MUBARIS-KT/DC-DC_CONVERTER/swg.png

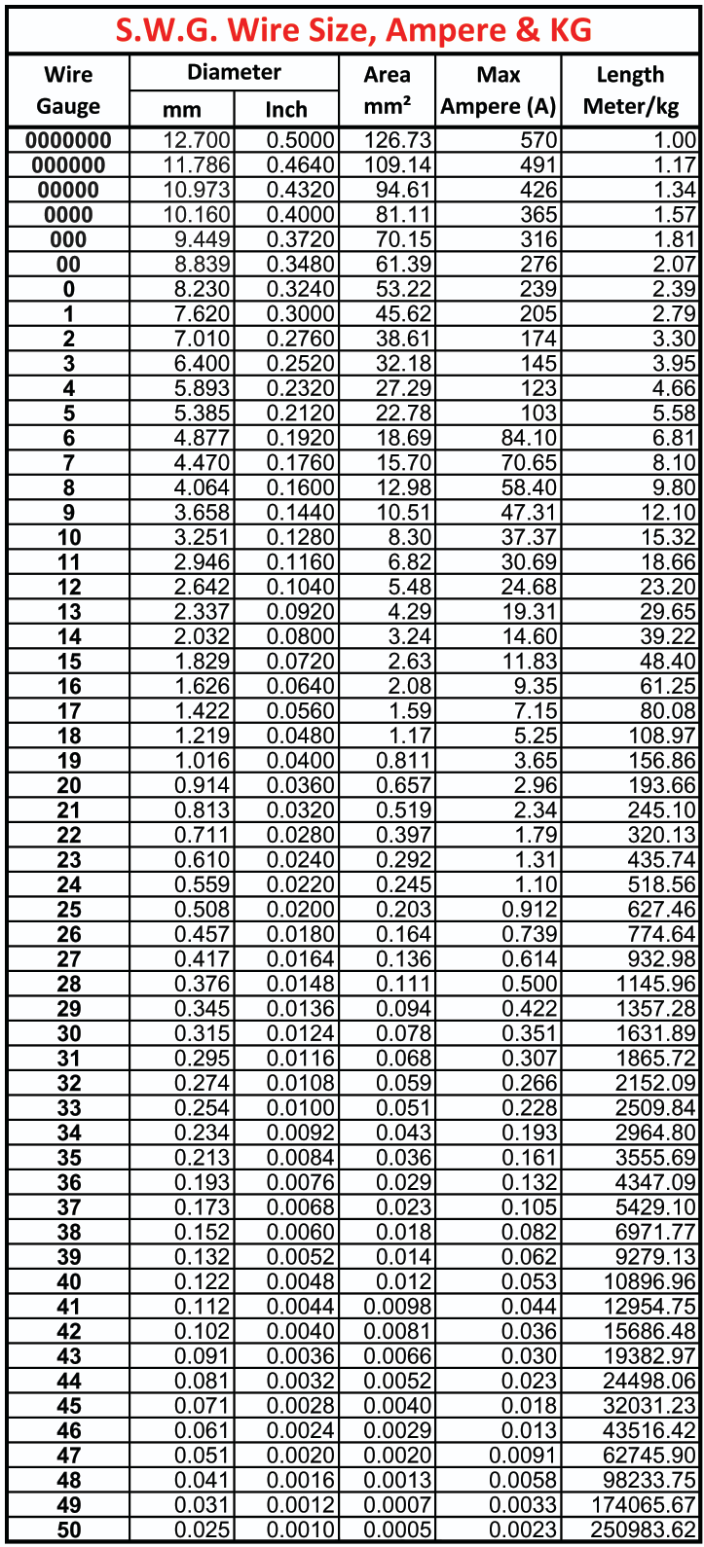
swg.png
