MUBARIS-KT/DC-DC_CONVERTER/SWG_chart.png

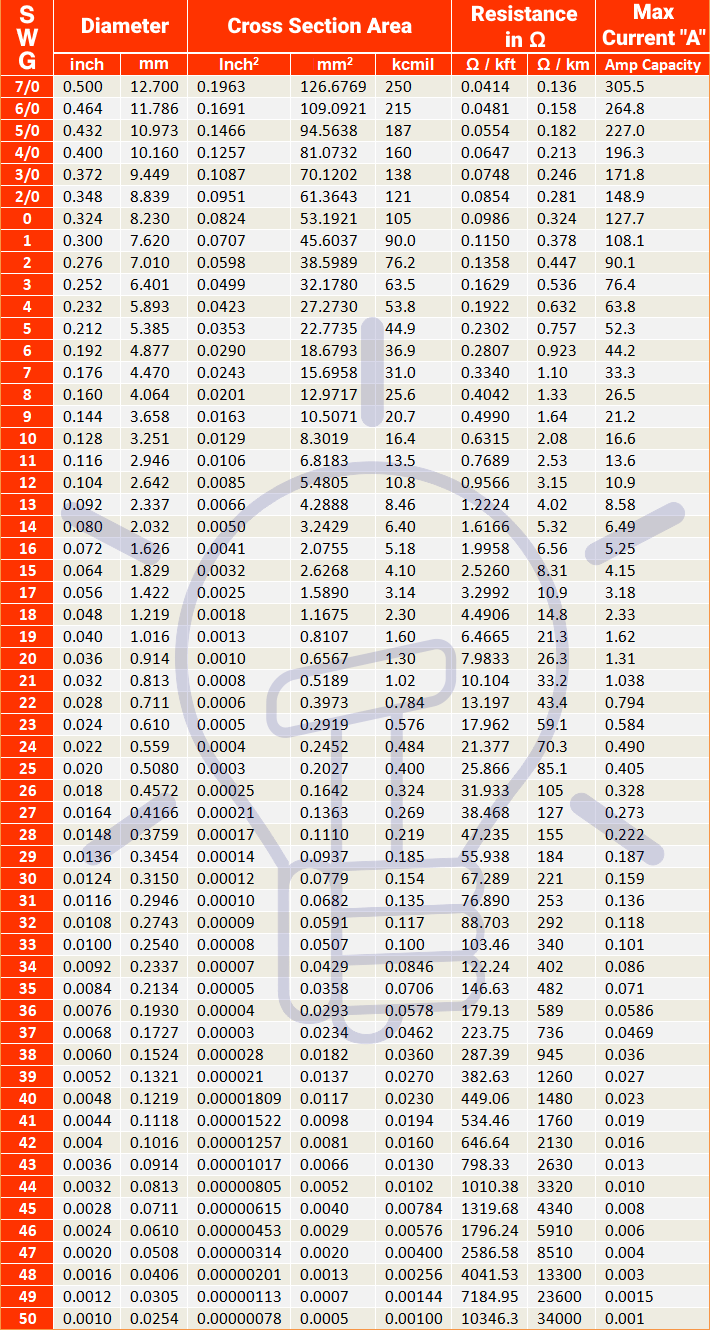
SWG_chart.png
