MUBARIS-KT/DC-DC_CONVERTER/Gate Driver TLP152 V1.1/sed.pdf

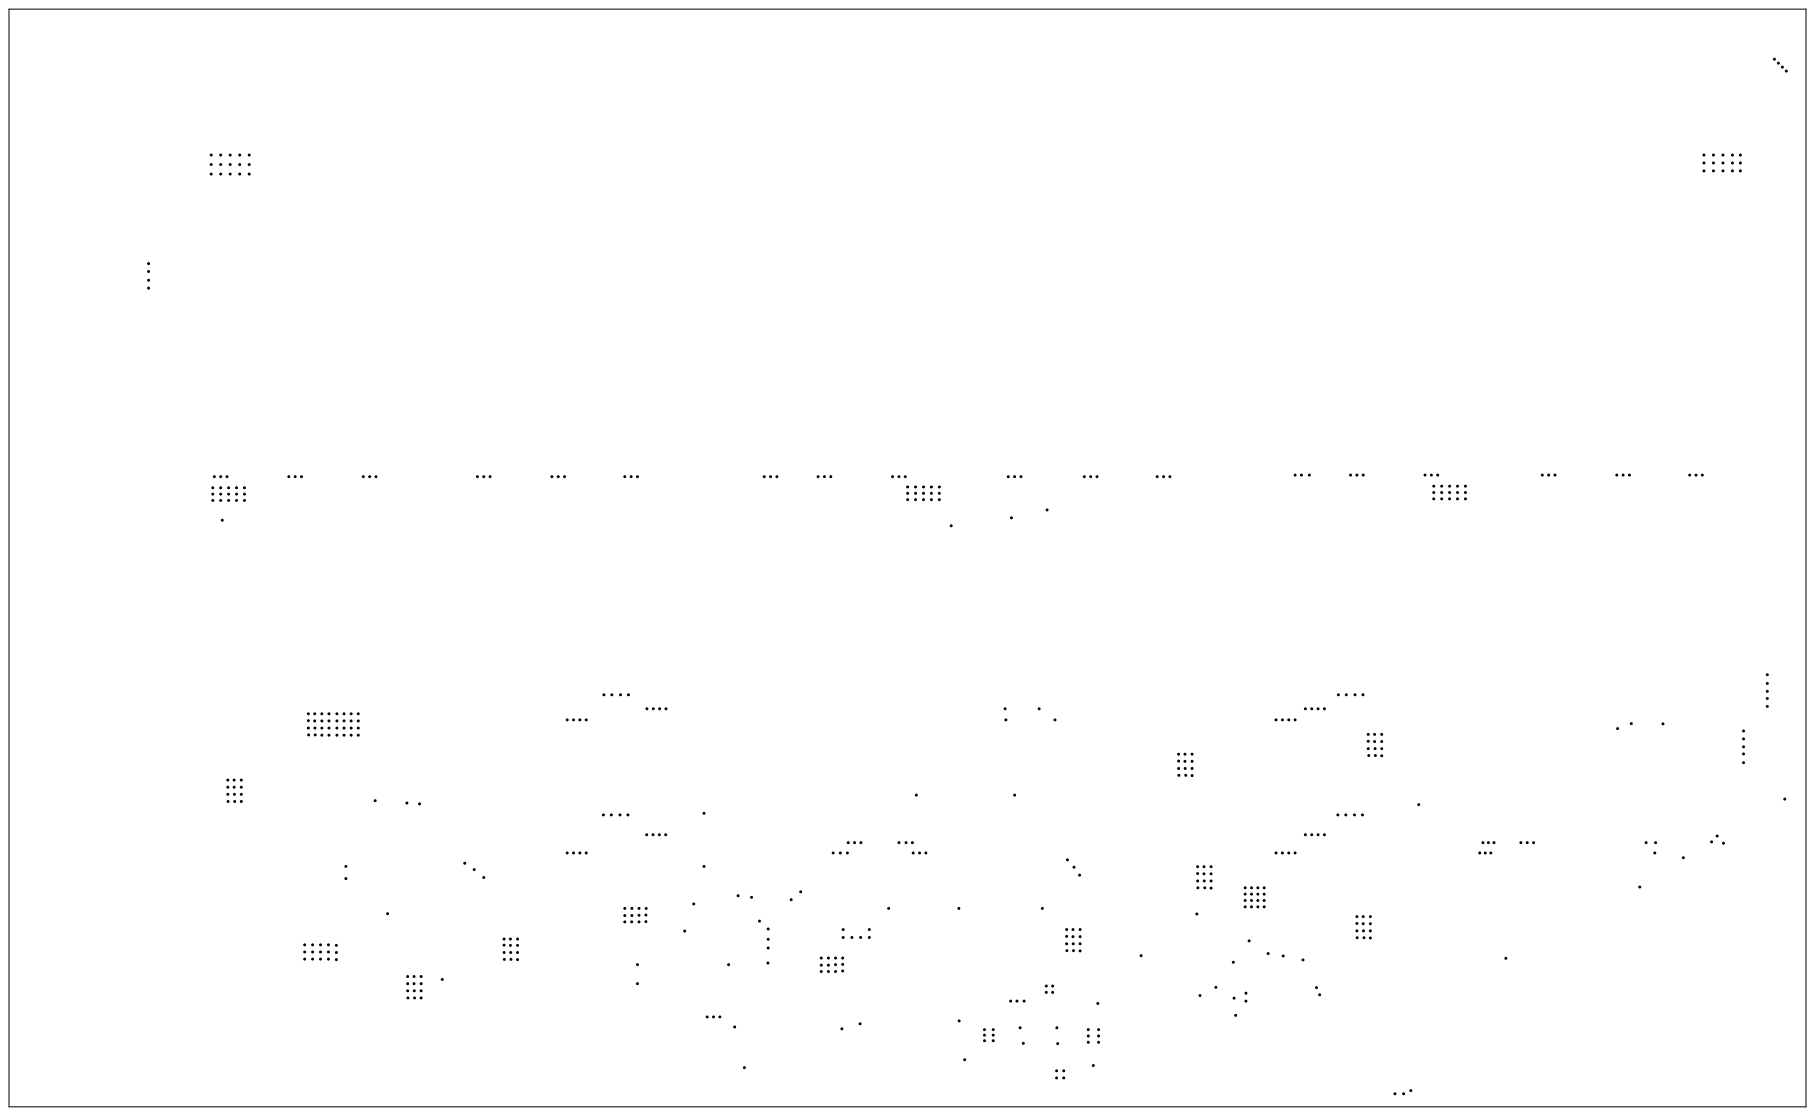
[picture p85: page 1]
