MUBARIS-KT/DC-DC_CONVERTER/PWM/pwm_ert_rtw/pwm.c

/*
 * Academic License - for use in teaching, academic research, and meeting
 * course requirements at degree granting institutions only.  Not for
 * government, commercial, or other organizational use.
 *
 * File: pwm.c
 *
 * Code generated for Simulink model 'pwm'.
 *
 * Model version                  : 1.6
 * Simulink Coder version         : 24.1 (R2024a) 19-Nov-2023
 * C/C++ source code generated on : Thu Aug  8 16:41:47 2024
 *
 * Target selection: ert.tlc
 * Embedded hardware selection: Texas Instruments->C2000
 * Code generation objectives: Unspecified
 * Validation result: Not run
 */

#include "pwm.h"
#include "rtwtypes.h"
#include "pwm_private.h"

/* Block signals (default storage) */
B_pwm_T pwm_B;

/* Real-time model */
static RT_MODEL_pwm_T pwm_M_;
RT_MODEL_pwm_T *const pwm_M = &pwm_M_;

#ifndef __TMS320C28XX_CLA__

uint16_T MW_adcBInitFlag = 0;

#endif

/* Model step function */
void pwm_step(void)
{
  real_T rtb_Sum;

  /* S-Function (c2802xadc): '<Root>/ADC' */
  {
    /*  Internal Reference Voltage : Fixed scale 0 to 3.3 V range.  */
    /*  External Reference Voltage : Allowable ranges of VREFHI(ADCINA0) = 3.3 and VREFLO(tied to ground) = 0  */
    AdcbRegs.ADCSOCFRC1.bit.SOC0 = 1U;

    /* Wait for the period of Sampling window and EOC result to be latched after trigger */
#ifndef __TMS320C28XX_CLA__

    asm(" RPT #75|| NOP");

#endif

#ifdef __TMS320C28XX_CLA__

    real32_T wait_index;
    for (wait_index= 12; wait_index > 0; wait_index--)
      __mnop();

#endif

    pwm_B.ADC = (AdcbResultRegs.ADCRESULT0);
  }

  /* Gain: '<Root>/Gain' */
  rtb_Sum = pwm_P.Gain_Gain * pwm_B.ADC;

  /* S-Function (c2802xpwm): '<Root>/ePWM' */

  /*-- Update CMPA value for ePWM1 --*/
  {
    EPwm1Regs.CMPA.bit.CMPA = (uint16_T)((uint32_T)EPwm1Regs.TBPRD * rtb_Sum *
      0.01);
  }

  /* Sum: '<Root>/Sum' incorporates:
   *  Constant: '<Root>/Constant'
   */
  rtb_Sum = pwm_P.Constant_Value - rtb_Sum;

  /* S-Function (c2802xpwm): '<Root>/ePWM1' */

  /*-- Update CMPA value for ePWM2 --*/
  {
    EPwm2Regs.CMPA.bit.CMPA = (uint16_T)((uint32_T)EPwm2Regs.TBPRD * rtb_Sum *
      0.01);
  }
}

/* Model initialize function */
void pwm_initialize(void)
{
  /* Registration code */

  /* initialize error status */
  rtmSetErrorStatus(pwm_M, (NULL));

  /* block I/O */
  (void) memset(((void *) &pwm_B), 0,
                sizeof(B_pwm_T));

  /* Start for S-Function (c2802xadc): '<Root>/ADC' */
  if (MW_adcBInitFlag == 0U) {
    InitAdcB();
    MW_adcBInitFlag = 1U;
  }

  config_ADCB_SOC0 ();

  /* Start for S-Function (c2802xpwm): '<Root>/ePWM' */

  /*** Initialize ePWM1 modules ***/
  {
    /*  // Time Base Control Register
       EPwm1Regs.TBCTL.bit.CTRMODE              = 2U;          // Counter Mode
       EPwm1Regs.TBCTL.bit.SYNCOSEL             = 1U;          // Sync Output Select

       EPwm1Regs.TBCTL.bit.PRDLD                = 0U;          // Shadow select

       EPwm1Regs.TBCTL2.bit.PRDLDSYNC           = 0U;          // Shadow select

       EPwm1Regs.TBCTL.bit.PHSEN                = 0U;          // Phase Load Enable
       EPwm1Regs.TBCTL.bit.PHSDIR               = 0U;          // Phase Direction Bit
       EPwm1Regs.TBCTL.bit.HSPCLKDIV            = 0U;          // High Speed TBCLK Pre-scaler
       EPwm1Regs.TBCTL.bit.CLKDIV               = 0U;          // Time Base Clock Pre-scaler
     */
    EPwm1Regs.TBCTL.all = (EPwm1Regs.TBCTL.all & ~0x3FFFU) | 0x12U;
    EPwm1Regs.TBCTL2.all = (EPwm1Regs.TBCTL2.all & ~0xC000U) | 0x0U;

    /*-- Setup Time-Base (TB) Submodule --*/
    EPwm1Regs.TBPRD = 1667U;           // Time Base Period Register

    /* // Time-Base Phase Register
       EPwm1Regs.TBPHS.bit.TBPHS               = 0U;          // Phase offset register
     */
    EPwm1Regs.TBPHS.all = (EPwm1Regs.TBPHS.all & ~0xFFFF0000U) | 0x0U;

    // Time Base Counter Register
    EPwm1Regs.TBCTR = 0x0000U;         /* Clear counter*/

    /*-- Setup Counter_Compare (CC) Submodule --*/
    /*	// Counter Compare Control Register

       EPwm1Regs.CMPCTL.bit.LOADASYNC           = 0U;          // Active Compare A Load SYNC Option
       EPwm1Regs.CMPCTL.bit.LOADBSYNC           = 0U;          // Active Compare B Load SYNC Option
       EPwm1Regs.CMPCTL.bit.LOADAMODE           = 0U;          // Active Compare A Load
       EPwm1Regs.CMPCTL.bit.LOADBMODE           = 0U;          // Active Compare B Load
       EPwm1Regs.CMPCTL.bit.SHDWAMODE           = 0U;          // Compare A Register Block Operating Mode
       EPwm1Regs.CMPCTL.bit.SHDWBMODE           = 0U;          // Compare B Register Block Operating Mode
     */
    EPwm1Regs.CMPCTL.all = (EPwm1Regs.CMPCTL.all & ~0x3C5FU) | 0x0U;

    /* EPwm1Regs.CMPCTL2.bit.SHDWCMODE           = 0U;          // Compare C Register Block Operating Mode
       EPwm1Regs.CMPCTL2.bit.SHDWDMODE           = 0U;          // Compare D Register Block Operating Mode
       EPwm1Regs.CMPCTL2.bit.LOADCSYNC           = 0U;          // Active Compare C Load SYNC Option
       EPwm1Regs.CMPCTL2.bit.LOADDSYNC           = 0U;          // Active Compare D Load SYNC Option
       EPwm1Regs.CMPCTL2.bit.LOADCMODE           = 0U;          // Active Compare C Load
       EPwm1Regs.CMPCTL2.bit.LOADDMODE           = 0U;          // Active Compare D Load
     */
    EPwm1Regs.CMPCTL2.all = (EPwm1Regs.CMPCTL2.all & ~0x3C5FU) | 0x0U;
    EPwm1Regs.CMPA.bit.CMPA = 833U;    // Counter Compare A Register
    EPwm1Regs.CMPB.bit.CMPB = 833U;    // Counter Compare B Register
    EPwm1Regs.CMPC = 32000U;           // Counter Compare C Register
    EPwm1Regs.CMPD = 32000U;           // Counter Compare D Register

    /*-- Setup Action-Qualifier (AQ) Submodule --*/
    EPwm1Regs.AQCTLA.all = 144U;
                               // Action Qualifier Control Register For Output A
    EPwm1Regs.AQCTLB.all = 144U;
                               // Action Qualifier Control Register For Output B

    /*	// Action Qualifier Software Force Register
       EPwm1Regs.AQSFRC.bit.RLDCSF              = 0U;          // Reload from Shadow Options
     */
    EPwm1Regs.AQSFRC.all = (EPwm1Regs.AQSFRC.all & ~0xC0U) | 0x0U;

    /*	// Action Qualifier Continuous S/W Force Register
       EPwm1Regs.AQCSFRC.bit.CSFA               = 0U;          // Continuous Software Force on output A
       EPwm1Regs.AQCSFRC.bit.CSFB               = 0U;          // Continuous Software Force on output B
     */
    EPwm1Regs.AQCSFRC.all = (EPwm1Regs.AQCSFRC.all & ~0xFU) | 0x0U;

    /*-- Setup Dead-Band Generator (DB) Submodule --*/
    /*	// Dead-Band Generator Control Register
       EPwm1Regs.DBCTL.bit.OUT_MODE             = 0U;          // Dead Band Output Mode Control
       EPwm1Regs.DBCTL.bit.IN_MODE              = 0U;          // Dead Band Input Select Mode Control
       EPwm1Regs.DBCTL.bit.POLSEL               = 0;          // Polarity Select Control
       EPwm1Regs.DBCTL.bit.HALFCYCLE            = 0U;          // Half Cycle Clocking Enable
       EPwm1Regs.DBCTL.bit.SHDWDBREDMODE        = 0U;          // DBRED shadow mode
       EPwm1Regs.DBCTL.bit.SHDWDBFEDMODE        = 0U;          // DBFED shadow mode
       EPwm1Regs.DBCTL.bit.LOADREDMODE          = 4U;        // DBRED load
       EPwm1Regs.DBCTL.bit.LOADFEDMODE          = 4U;        // DBFED load
     */
    EPwm1Regs.DBCTL.all = (EPwm1Regs.DBCTL.all & ~0x8FFFU) | 0x0U;
    EPwm1Regs.DBRED.bit.DBRED = (uint16_T)(0);
                         // Dead-Band Generator Rising Edge Delay Count Register
    EPwm1Regs.DBFED.bit.DBFED = (uint16_T)(0);
                        // Dead-Band Generator Falling Edge Delay Count Register

    /*-- Setup Event-Trigger (ET) Submodule --*/
    /*	// Event Trigger Selection and Pre-Scale Register
       EPwm1Regs.ETSEL.bit.SOCAEN               = 0U;          // Start of Conversion A Enable
       EPwm1Regs.ETSEL.bit.SOCASELCMP           = 0U;
       EPwm1Regs.ETSEL.bit.SOCASEL              = 1U;          // Start of Conversion A Select
       EPwm1Regs.ETPS.bit.SOCPSSEL              = 1U;          // EPWM1SOC Period Select
       EPwm1Regs.ETSOCPS.bit.SOCAPRD2           = 1U;
       EPwm1Regs.ETSEL.bit.SOCBEN               = 0U;          // Start of Conversion B Enable
       EPwm1Regs.ETSEL.bit.SOCBSELCMP           = 0U;
       EPwm1Regs.ETSEL.bit.SOCBSEL              = 1U;          // Start of Conversion A Select
       EPwm1Regs.ETPS.bit.SOCPSSEL              = 1;          // EPWM1SOCB Period Select
       EPwm1Regs.ETSOCPS.bit.SOCBPRD2           = 1U;
       EPwm1Regs.ETSEL.bit.INTEN                = 0U;          // EPWM1INTn Enable
       EPwm1Regs.ETSEL.bit.INTSELCMP            = 0U;
       EPwm1Regs.ETSEL.bit.INTSEL               = 1U;          // Start of Conversion A Select
       EPwm1Regs.ETPS.bit.INTPSSEL              = 1U;          // EPWM1INTn Period Select
       EPwm1Regs.ETINTPS.bit.INTPRD2            = 1U;
     */
    EPwm1Regs.ETSEL.all = (EPwm1Regs.ETSEL.all & ~0xFF7FU) | 0x1101U;
    EPwm1Regs.ETPS.all = (EPwm1Regs.ETPS.all & ~0x30U) | 0x30U;
    EPwm1Regs.ETSOCPS.all = (EPwm1Regs.ETSOCPS.all & ~0xF0FU) | 0x101U;
    EPwm1Regs.ETINTPS.all = (EPwm1Regs.ETINTPS.all & ~0xFU) | 0x1U;

    /*-- Setup PWM-Chopper (PC) Submodule --*/
    /*	// PWM Chopper Control Register
       EPwm1Regs.PCCTL.bit.CHPEN                = 0U;          // PWM chopping enable
       EPwm1Regs.PCCTL.bit.CHPFREQ              = 0U;          // Chopping clock frequency
       EPwm1Regs.PCCTL.bit.OSHTWTH              = 0U;          // One-shot pulse width
       EPwm1Regs.PCCTL.bit.CHPDUTY              = 0U;          // Chopping clock Duty cycle
     */
    EPwm1Regs.PCCTL.all = (EPwm1Regs.PCCTL.all & ~0x7FFU) | 0x0U;

    /*-- Set up Trip-Zone (TZ) Submodule --*/
    EALLOW;
    EPwm1Regs.TZSEL.all = 0U;          // Trip Zone Select Register

    /*	// Trip Zone Control Register
       EPwm1Regs.TZCTL.bit.TZA                  = 3U;          // TZ1 to TZ6 Trip Action On EPWM1A
       EPwm1Regs.TZCTL.bit.TZB                  = 3U;          // TZ1 to TZ6 Trip Action On EPWM1B
       EPwm1Regs.TZCTL.bit.DCAEVT1              = 3U;          // EPWM1A action on DCAEVT1
       EPwm1Regs.TZCTL.bit.DCAEVT2              = 3U;          // EPWM1A action on DCAEVT2
       EPwm1Regs.TZCTL.bit.DCBEVT1              = 3U;          // EPWM1B action on DCBEVT1
       EPwm1Regs.TZCTL.bit.DCBEVT2              = 3U;          // EPWM1B action on DCBEVT2
     */
    EPwm1Regs.TZCTL.all = (EPwm1Regs.TZCTL.all & ~0xFFFU) | 0xFFFU;

    /*	// Trip Zone Enable Interrupt Register
       EPwm1Regs.TZEINT.bit.OST                 = 0U;          // Trip Zones One Shot Int Enable
       EPwm1Regs.TZEINT.bit.CBC                 = 0U;          // Trip Zones Cycle By Cycle Int Enable
       EPwm1Regs.TZEINT.bit.DCAEVT1             = 0U;          // Digital Compare A Event 1 Int Enable
       EPwm1Regs.TZEINT.bit.DCAEVT2             = 0U;          // Digital Compare A Event 2 Int Enable
       EPwm1Regs.TZEINT.bit.DCBEVT1             = 0U;          // Digital Compare B Event 1 Int Enable
       EPwm1Regs.TZEINT.bit.DCBEVT2             = 0U;          // Digital Compare B Event 2 Int Enable
     */
    EPwm1Regs.TZEINT.all = (EPwm1Regs.TZEINT.all & ~0x7EU) | 0x0U;

    /*	// Digital Compare A Control Register
       EPwm1Regs.DCACTL.bit.EVT1SYNCE           = 0U;          // DCAEVT1 SYNC Enable
       EPwm1Regs.DCACTL.bit.EVT1SOCE            = 1U;          // DCAEVT1 SOC Enable
       EPwm1Regs.DCACTL.bit.EVT1FRCSYNCSEL      = 0U;          // DCAEVT1 Force Sync Signal
       EPwm1Regs.DCACTL.bit.EVT1SRCSEL          = 0U;          // DCAEVT1 Source Signal
       EPwm1Regs.DCACTL.bit.EVT2FRCSYNCSEL      = 0U;          // DCAEVT2 Force Sync Signal
       EPwm1Regs.DCACTL.bit.EVT2SRCSEL          = 0U;          // DCAEVT2 Source Signal
     */
    EPwm1Regs.DCACTL.all = (EPwm1Regs.DCACTL.all & ~0x30FU) | 0x4U;

    /*	// Digital Compare B Control Register
       EPwm1Regs.DCBCTL.bit.EVT1SYNCE           = 0U;          // DCBEVT1 SYNC Enable
       EPwm1Regs.DCBCTL.bit.EVT1SOCE            = 0U;          // DCBEVT1 SOC Enable
       EPwm1Regs.DCBCTL.bit.EVT1FRCSYNCSEL      = 0U;          // DCBEVT1 Force Sync Signal
       EPwm1Regs.DCBCTL.bit.EVT1SRCSEL          = 0U;          // DCBEVT1 Source Signal
       EPwm1Regs.DCBCTL.bit.EVT2FRCSYNCSEL      = 0U;          // DCBEVT2 Force Sync Signal
       EPwm1Regs.DCBCTL.bit.EVT2SRCSEL          = 0U;          // DCBEVT2 Source Signal
     */
    EPwm1Regs.DCBCTL.all = (EPwm1Regs.DCBCTL.all & ~0x30FU) | 0x0U;

    /*	// Digital Compare Trip Select Register
       EPwm1Regs.DCTRIPSEL.bit.DCAHCOMPSEL      = 0U;          // Digital Compare A High COMP Input Select

       EPwm1Regs.DCTRIPSEL.bit.DCALCOMPSEL      = 0U;          // Digital Compare A Low COMP Input Select
       EPwm1Regs.DCTRIPSEL.bit.DCBHCOMPSEL      = 0U;          // Digital Compare B High COMP Input Select
       EPwm1Regs.DCTRIPSEL.bit.DCBLCOMPSEL      = 0U;          // Digital Compare B Low COMP Input Select
     */
    EPwm1Regs.DCTRIPSEL.all = (EPwm1Regs.DCTRIPSEL.all & ~ 0xFFFFU) | 0x0U;

    /*	// Trip Zone Digital Comparator Select Register
       EPwm1Regs.TZDCSEL.bit.DCAEVT1            = 0U;          // Digital Compare Output A Event 1
       EPwm1Regs.TZDCSEL.bit.DCAEVT2            = 0U;          // Digital Compare Output A Event 2
       EPwm1Regs.TZDCSEL.bit.DCBEVT1            = 0U;          // Digital Compare Output B Event 1
       EPwm1Regs.TZDCSEL.bit.DCBEVT2            = 0U;          // Digital Compare Output B Event 2
     */
    EPwm1Regs.TZDCSEL.all = (EPwm1Regs.TZDCSEL.all & ~0xFFFU) | 0x0U;

    /*	// Digital Compare Filter Control Register
       EPwm1Regs.DCFCTL.bit.BLANKE              = 0U;          // Blanking Enable/Disable
       EPwm1Regs.DCFCTL.bit.PULSESEL            = 1U;          // Pulse Select for Blanking & Capture Alignment
       EPwm1Regs.DCFCTL.bit.BLANKINV            = 0U;          // Blanking Window Inversion
       EPwm1Regs.DCFCTL.bit.SRCSEL              = 0U;          // Filter Block Signal Source Select
     */
    EPwm1Regs.DCFCTL.all = (EPwm1Regs.DCFCTL.all & ~0x3FU) | 0x10U;
    EPwm1Regs.DCFOFFSET = 0U;          // Digital Compare Filter Offset Register
    EPwm1Regs.DCFWINDOW = 0U;          // Digital Compare Filter Window Register

    /*	// Digital Compare Capture Control Register
       EPwm1Regs.DCCAPCTL.bit.CAPE              = 0U;          // Counter Capture Enable
     */
    EPwm1Regs.DCCAPCTL.all = (EPwm1Regs.DCCAPCTL.all & ~0x1U) | 0x0U;

    /*	// HRPWM Configuration Register
       EPwm1Regs.HRCNFG.bit.SWAPAB              = 0U;          // Swap EPWMA and EPWMB Outputs Bit
       EPwm1Regs.HRCNFG.bit.SELOUTB             = 0U;          // EPWMB Output Selection Bit
     */
    EPwm1Regs.HRCNFG.all = (EPwm1Regs.HRCNFG.all & ~0xA0U) | 0x0U;

    /* Update the Link Registers with the link value for all the Compare values and TBPRD */
    /* No error is thrown if the ePWM register exists in the model or not */
    EPwm1Regs.EPWMXLINK.bit.TBPRDLINK = 0U;
    EPwm1Regs.EPWMXLINK.bit.CMPALINK = 0U;
    EPwm1Regs.EPWMXLINK.bit.CMPBLINK = 0U;
    EPwm1Regs.EPWMXLINK.bit.CMPCLINK = 0U;
    EPwm1Regs.EPWMXLINK.bit.CMPDLINK = 0U;

    /* SYNCPER - Peripheral synchronization output event
       EPwm1Regs.HRPCTL.bit.PWMSYNCSEL            = 1U;          // EPWMSYNCPER selection
       EPwm1Regs.HRPCTL.bit.PWMSYNCSELX           = 0U;          //  EPWMSYNCPER selection
     */
    EPwm1Regs.HRPCTL.all = (EPwm1Regs.HRPCTL.all & ~0x72U) | 0x2U;
    EDIS;
  }

  /* Start for S-Function (c2802xpwm): '<Root>/ePWM1' */

  /*** Initialize ePWM2 modules ***/
  {
    /*  // Time Base Control Register
       EPwm2Regs.TBCTL.bit.CTRMODE              = 2U;          // Counter Mode
       EPwm2Regs.TBCTL.bit.SYNCOSEL             = 0U;          // Sync Output Select

       EPwm2Regs.TBCTL.bit.PRDLD                = 0U;          // Shadow select

       EPwm2Regs.TBCTL2.bit.PRDLDSYNC           = 0U;          // Shadow select

       EPwm2Regs.TBCTL.bit.PHSEN                = 1U;          // Phase Load Enable
       EPwm2Regs.TBCTL.bit.PHSDIR               = 1U;          // Phase Direction Bit
       EPwm2Regs.TBCTL.bit.HSPCLKDIV            = 0U;          // High Speed TBCLK Pre-scaler
       EPwm2Regs.TBCTL.bit.CLKDIV               = 0U;          // Time Base Clock Pre-scaler
     */
    EPwm2Regs.TBCTL.all = (EPwm2Regs.TBCTL.all & ~0x3FFFU) | 0x2006U;
    EPwm2Regs.TBCTL2.all = (EPwm2Regs.TBCTL2.all & ~0xC000U) | 0x0U;

    /*-- Setup Time-Base (TB) Submodule --*/
    EPwm2Regs.TBPRD = 1667U;           // Time Base Period Register

    /* // Time-Base Phase Register
       EPwm2Regs.TBPHS.bit.TBPHS               = 0U;          // Phase offset register
     */
    EPwm2Regs.TBPHS.all = (EPwm2Regs.TBPHS.all & ~0xFFFF0000U) | 0x0U;

    // Time Base Counter Register
    EPwm2Regs.TBCTR = 0x0000U;         /* Clear counter*/

    /*-- Setup Counter_Compare (CC) Submodule --*/
    /*	// Counter Compare Control Register

       EPwm2Regs.CMPCTL.bit.LOADASYNC           = 0U;          // Active Compare A Load SYNC Option
       EPwm2Regs.CMPCTL.bit.LOADBSYNC           = 0U;          // Active Compare B Load SYNC Option
       EPwm2Regs.CMPCTL.bit.LOADAMODE           = 0U;          // Active Compare A Load
       EPwm2Regs.CMPCTL.bit.LOADBMODE           = 0U;          // Active Compare B Load
       EPwm2Regs.CMPCTL.bit.SHDWAMODE           = 0U;          // Compare A Register Block Operating Mode
       EPwm2Regs.CMPCTL.bit.SHDWBMODE           = 0U;          // Compare B Register Block Operating Mode
     */
    EPwm2Regs.CMPCTL.all = (EPwm2Regs.CMPCTL.all & ~0x3C5FU) | 0x0U;

    /* EPwm2Regs.CMPCTL2.bit.SHDWCMODE           = 0U;          // Compare C Register Block Operating Mode
       EPwm2Regs.CMPCTL2.bit.SHDWDMODE           = 0U;          // Compare D Register Block Operating Mode
       EPwm2Regs.CMPCTL2.bit.LOADCSYNC           = 0U;          // Active Compare C Load SYNC Option
       EPwm2Regs.CMPCTL2.bit.LOADDSYNC           = 0U;          // Active Compare D Load SYNC Option
       EPwm2Regs.CMPCTL2.bit.LOADCMODE           = 0U;          // Active Compare C Load
       EPwm2Regs.CMPCTL2.bit.LOADDMODE           = 0U;          // Active Compare D Load
     */
    EPwm2Regs.CMPCTL2.all = (EPwm2Regs.CMPCTL2.all & ~0x3C5FU) | 0x0U;
    EPwm2Regs.CMPA.bit.CMPA = 833U;    // Counter Compare A Register
    EPwm2Regs.CMPB.bit.CMPB = 833U;    // Counter Compare B Register
    EPwm2Regs.CMPC = 32000U;           // Counter Compare C Register
    EPwm2Regs.CMPD = 32000U;           // Counter Compare D Register

    /*-- Setup Action-Qualifier (AQ) Submodule --*/
    EPwm2Regs.AQCTLA.all = 96U;// Action Qualifier Control Register For Output A
    EPwm2Regs.AQCTLB.all = 96U;// Action Qualifier Control Register For Output B

    /*	// Action Qualifier Software Force Register
       EPwm2Regs.AQSFRC.bit.RLDCSF              = 0U;          // Reload from Shadow Options
     */
    EPwm2Regs.AQSFRC.all = (EPwm2Regs.AQSFRC.all & ~0xC0U) | 0x0U;

    /*	// Action Qualifier Continuous S/W Force Register
       EPwm2Regs.AQCSFRC.bit.CSFA               = 0U;          // Continuous Software Force on output A
       EPwm2Regs.AQCSFRC.bit.CSFB               = 0U;          // Continuous Software Force on output B
     */
    EPwm2Regs.AQCSFRC.all = (EPwm2Regs.AQCSFRC.all & ~0xFU) | 0x0U;

    /*-- Setup Dead-Band Generator (DB) Submodule --*/
    /*	// Dead-Band Generator Control Register
       EPwm2Regs.DBCTL.bit.OUT_MODE             = 0U;          // Dead Band Output Mode Control
       EPwm2Regs.DBCTL.bit.IN_MODE              = 0U;          // Dead Band Input Select Mode Control
       EPwm2Regs.DBCTL.bit.POLSEL               = 0;          // Polarity Select Control
       EPwm2Regs.DBCTL.bit.HALFCYCLE            = 0U;          // Half Cycle Clocking Enable
       EPwm2Regs.DBCTL.bit.SHDWDBREDMODE        = 0U;          // DBRED shadow mode
       EPwm2Regs.DBCTL.bit.SHDWDBFEDMODE        = 0U;          // DBFED shadow mode
       EPwm2Regs.DBCTL.bit.LOADREDMODE          = 4U;        // DBRED load
       EPwm2Regs.DBCTL.bit.LOADFEDMODE          = 4U;        // DBFED load
     */
    EPwm2Regs.DBCTL.all = (EPwm2Regs.DBCTL.all & ~0x8FFFU) | 0x0U;
    EPwm2Regs.DBRED.bit.DBRED = (uint16_T)(0);
                         // Dead-Band Generator Rising Edge Delay Count Register
    EPwm2Regs.DBFED.bit.DBFED = (uint16_T)(0);
                        // Dead-Band Generator Falling Edge Delay Count Register

    /*-- Setup Event-Trigger (ET) Submodule --*/
    /*	// Event Trigger Selection and Pre-Scale Register
       EPwm2Regs.ETSEL.bit.SOCAEN               = 0U;          // Start of Conversion A Enable
       EPwm2Regs.ETSEL.bit.SOCASELCMP           = 0U;
       EPwm2Regs.ETSEL.bit.SOCASEL              = 1U;          // Start of Conversion A Select
       EPwm2Regs.ETPS.bit.SOCPSSEL              = 1U;          // EPWM2SOC Period Select
       EPwm2Regs.ETSOCPS.bit.SOCAPRD2           = 1U;
       EPwm2Regs.ETSEL.bit.SOCBEN               = 0U;          // Start of Conversion B Enable
       EPwm2Regs.ETSEL.bit.SOCBSELCMP           = 0U;
       EPwm2Regs.ETSEL.bit.SOCBSEL              = 1U;          // Start of Conversion A Select
       EPwm2Regs.ETPS.bit.SOCPSSEL              = 1;          // EPWM2SOCB Period Select
       EPwm2Regs.ETSOCPS.bit.SOCBPRD2           = 1U;
       EPwm2Regs.ETSEL.bit.INTEN                = 0U;          // EPWM2INTn Enable
       EPwm2Regs.ETSEL.bit.INTSELCMP            = 0U;
       EPwm2Regs.ETSEL.bit.INTSEL               = 1U;          // Start of Conversion A Select
       EPwm2Regs.ETPS.bit.INTPSSEL              = 1U;          // EPWM2INTn Period Select
       EPwm2Regs.ETINTPS.bit.INTPRD2            = 1U;
     */
    EPwm2Regs.ETSEL.all = (EPwm2Regs.ETSEL.all & ~0xFF7FU) | 0x1101U;
    EPwm2Regs.ETPS.all = (EPwm2Regs.ETPS.all & ~0x30U) | 0x30U;
    EPwm2Regs.ETSOCPS.all = (EPwm2Regs.ETSOCPS.all & ~0xF0FU) | 0x101U;
    EPwm2Regs.ETINTPS.all = (EPwm2Regs.ETINTPS.all & ~0xFU) | 0x1U;

    /*-- Setup PWM-Chopper (PC) Submodule --*/
    /*	// PWM Chopper Control Register
       EPwm2Regs.PCCTL.bit.CHPEN                = 0U;          // PWM chopping enable
       EPwm2Regs.PCCTL.bit.CHPFREQ              = 0U;          // Chopping clock frequency
       EPwm2Regs.PCCTL.bit.OSHTWTH              = 0U;          // One-shot pulse width
       EPwm2Regs.PCCTL.bit.CHPDUTY              = 0U;          // Chopping clock Duty cycle
     */
    EPwm2Regs.PCCTL.all = (EPwm2Regs.PCCTL.all & ~0x7FFU) | 0x0U;

    /*-- Set up Trip-Zone (TZ) Submodule --*/
    EALLOW;
    EPwm2Regs.TZSEL.all = 0U;          // Trip Zone Select Register

    /*	// Trip Zone Control Register
       EPwm2Regs.TZCTL.bit.TZA                  = 3U;          // TZ1 to TZ6 Trip Action On EPWM2A
       EPwm2Regs.TZCTL.bit.TZB                  = 3U;          // TZ1 to TZ6 Trip Action On EPWM2B
       EPwm2Regs.TZCTL.bit.DCAEVT1              = 3U;          // EPWM2A action on DCAEVT1
       EPwm2Regs.TZCTL.bit.DCAEVT2              = 3U;          // EPWM2A action on DCAEVT2
       EPwm2Regs.TZCTL.bit.DCBEVT1              = 3U;          // EPWM2B action on DCBEVT1
       EPwm2Regs.TZCTL.bit.DCBEVT2              = 3U;          // EPWM2B action on DCBEVT2
     */
    EPwm2Regs.TZCTL.all = (EPwm2Regs.TZCTL.all & ~0xFFFU) | 0xFFFU;

    /*	// Trip Zone Enable Interrupt Register
       EPwm2Regs.TZEINT.bit.OST                 = 0U;          // Trip Zones One Shot Int Enable
       EPwm2Regs.TZEINT.bit.CBC                 = 0U;          // Trip Zones Cycle By Cycle Int Enable
       EPwm2Regs.TZEINT.bit.DCAEVT1             = 0U;          // Digital Compare A Event 1 Int Enable
       EPwm2Regs.TZEINT.bit.DCAEVT2             = 0U;          // Digital Compare A Event 2 Int Enable
       EPwm2Regs.TZEINT.bit.DCBEVT1             = 0U;          // Digital Compare B Event 1 Int Enable
       EPwm2Regs.TZEINT.bit.DCBEVT2             = 0U;          // Digital Compare B Event 2 Int Enable
     */
    EPwm2Regs.TZEINT.all = (EPwm2Regs.TZEINT.all & ~0x7EU) | 0x0U;

    /*	// Digital Compare A Control Register
       EPwm2Regs.DCACTL.bit.EVT1SYNCE           = 0U;          // DCAEVT1 SYNC Enable
       EPwm2Regs.DCACTL.bit.EVT1SOCE            = 1U;          // DCAEVT1 SOC Enable
       EPwm2Regs.DCACTL.bit.EVT1FRCSYNCSEL      = 0U;          // DCAEVT1 Force Sync Signal
       EPwm2Regs.DCACTL.bit.EVT1SRCSEL          = 0U;          // DCAEVT1 Source Signal
       EPwm2Regs.DCACTL.bit.EVT2FRCSYNCSEL      = 0U;          // DCAEVT2 Force Sync Signal
       EPwm2Regs.DCACTL.bit.EVT2SRCSEL          = 0U;          // DCAEVT2 Source Signal
     */
    EPwm2Regs.DCACTL.all = (EPwm2Regs.DCACTL.all & ~0x30FU) | 0x4U;

    /*	// Digital Compare B Control Register
       EPwm2Regs.DCBCTL.bit.EVT1SYNCE           = 0U;          // DCBEVT1 SYNC Enable
       EPwm2Regs.DCBCTL.bit.EVT1SOCE            = 0U;          // DCBEVT1 SOC Enable
       EPwm2Regs.DCBCTL.bit.EVT1FRCSYNCSEL      = 0U;          // DCBEVT1 Force Sync Signal
       EPwm2Regs.DCBCTL.bit.EVT1SRCSEL          = 0U;          // DCBEVT1 Source Signal
       EPwm2Regs.DCBCTL.bit.EVT2FRCSYNCSEL      = 0U;          // DCBEVT2 Force Sync Signal
       EPwm2Regs.DCBCTL.bit.EVT2SRCSEL          = 0U;          // DCBEVT2 Source Signal
     */
    EPwm2Regs.DCBCTL.all = (EPwm2Regs.DCBCTL.all & ~0x30FU) | 0x0U;

    /*	// Digital Compare Trip Select Register
       EPwm2Regs.DCTRIPSEL.bit.DCAHCOMPSEL      = 0U;          // Digital Compare A High COMP Input Select

       EPwm2Regs.DCTRIPSEL.bit.DCALCOMPSEL      = 0U;          // Digital Compare A Low COMP Input Select
       EPwm2Regs.DCTRIPSEL.bit.DCBHCOMPSEL      = 0U;          // Digital Compare B High COMP Input Select
       EPwm2Regs.DCTRIPSEL.bit.DCBLCOMPSEL      = 0U;          // Digital Compare B Low COMP Input Select
     */
    EPwm2Regs.DCTRIPSEL.all = (EPwm2Regs.DCTRIPSEL.all & ~ 0xFFFFU) | 0x0U;

    /*	// Trip Zone Digital Comparator Select Register
       EPwm2Regs.TZDCSEL.bit.DCAEVT1            = 0U;          // Digital Compare Output A Event 1
       EPwm2Regs.TZDCSEL.bit.DCAEVT2            = 0U;          // Digital Compare Output A Event 2
       EPwm2Regs.TZDCSEL.bit.DCBEVT1            = 0U;          // Digital Compare Output B Event 1
       EPwm2Regs.TZDCSEL.bit.DCBEVT2            = 0U;          // Digital Compare Output B Event 2
     */
    EPwm2Regs.TZDCSEL.all = (EPwm2Regs.TZDCSEL.all & ~0xFFFU) | 0x0U;

    /*	// Digital Compare Filter Control Register
       EPwm2Regs.DCFCTL.bit.BLANKE              = 0U;          // Blanking Enable/Disable
       EPwm2Regs.DCFCTL.bit.PULSESEL            = 1U;          // Pulse Select for Blanking & Capture Alignment
       EPwm2Regs.DCFCTL.bit.BLANKINV            = 0U;          // Blanking Window Inversion
       EPwm2Regs.DCFCTL.bit.SRCSEL              = 0U;          // Filter Block Signal Source Select
     */
    EPwm2Regs.DCFCTL.all = (EPwm2Regs.DCFCTL.all & ~0x3FU) | 0x10U;
    EPwm2Regs.DCFOFFSET = 0U;          // Digital Compare Filter Offset Register
    EPwm2Regs.DCFWINDOW = 0U;          // Digital Compare Filter Window Register

    /*	// Digital Compare Capture Control Register
       EPwm2Regs.DCCAPCTL.bit.CAPE              = 0U;          // Counter Capture Enable
     */
    EPwm2Regs.DCCAPCTL.all = (EPwm2Regs.DCCAPCTL.all & ~0x1U) | 0x0U;

    /*	// HRPWM Configuration Register
       EPwm2Regs.HRCNFG.bit.SWAPAB              = 0U;          // Swap EPWMA and EPWMB Outputs Bit
       EPwm2Regs.HRCNFG.bit.SELOUTB             = 0U;          // EPWMB Output Selection Bit
     */
    EPwm2Regs.HRCNFG.all = (EPwm2Regs.HRCNFG.all & ~0xA0U) | 0x0U;

    /* Update the Link Registers with the link value for all the Compare values and TBPRD */
    /* No error is thrown if the ePWM register exists in the model or not */
    EPwm2Regs.EPWMXLINK.bit.TBPRDLINK = 1U;
    EPwm2Regs.EPWMXLINK.bit.CMPALINK = 1U;
    EPwm2Regs.EPWMXLINK.bit.CMPBLINK = 1U;
    EPwm2Regs.EPWMXLINK.bit.CMPCLINK = 1U;
    EPwm2Regs.EPWMXLINK.bit.CMPDLINK = 1U;

    /* SYNCPER - Peripheral synchronization output event
       EPwm2Regs.HRPCTL.bit.PWMSYNCSEL            = 0U;          // EPWMSYNCPER selection
       EPwm2Regs.HRPCTL.bit.PWMSYNCSELX           = 0U;          //  EPWMSYNCPER selection
     */
    EPwm2Regs.HRPCTL.all = (EPwm2Regs.HRPCTL.all & ~0x72U) | 0x0U;
    EDIS;
  }
}

/* Model terminate function */
void pwm_terminate(void)
{
  /* (no terminate code required) */
}

/*
 * File trailer for generated code.
 *
 * [EOF]
 */
