MUBARIS-KT/DC-DC_CONVERTER/matlab files/pwm_ert_rtw/rtwtypes.h

/*
 * Academic License - for use in teaching, academic research, and meeting
 * course requirements at degree granting institutions only.  Not for
 * government, commercial, or other organizational use.
 *
 * File: rtwtypes.h
 *
 * Code generated for Simulink model 'pwm'.
 *
 * Model version                  : 1.7
 * Simulink Coder version         : 24.1 (R2024a) 19-Nov-2023
 * C/C++ source code generated on : Tue Sep 17 13:06:12 2024
 *
 * Target selection: ert.tlc
 * Embedded hardware selection: Texas Instruments->C2000
 * Code generation objectives: Unspecified
 * Validation result: Not run
 */

#ifndef RTWTYPES_H
#define RTWTYPES_H

/* Logical type definitions */
#if (!defined(__cplusplus))
#ifndef false
#define false                          (0U)
#endif

#ifndef true
#define true                           (1U)
#endif
#endif

/*=======================================================================*
 * Target hardware information
 *   Device type: Texas Instruments->C2000
 *   Number of bits:     char:  16    short:   16    int:  16
 *                       long:  32    long long:  64
 *                       native word size:  16
 *   Byte ordering: LittleEndian
 *   Signed integer division rounds to: Zero
 *   Shift right on a signed integer as arithmetic shift: on
 *=======================================================================*/

/*=======================================================================*
 * Fixed width word size data types:                                     *
 *   int8_T, int16_T, int32_T     - signed 8, 16, or 32 bit integers     *
 *   uint8_T, uint16_T, uint32_T  - unsigned 8, 16, or 32 bit integers   *
 *   real32_T, real64_T           - 32 and 64 bit floating point numbers *
 *                                                                       *
 *                                                                       *
 *   Note:  Because the specified hardware does not have native support  *
 *          for all data sizes, some data types are actually typedef'ed  *
 *          from larger native data sizes.  The following data types are *
 *          not in the ideal native data types:                          *
 *                                                                       *
 *          int8_T, uint8_T                                              *
 *=======================================================================*/
typedef int int8_T;
typedef unsigned int uint8_T;
typedef int int16_T;
typedef unsigned int uint16_T;
typedef long int32_T;
typedef unsigned long uint32_T;
typedef long long int64_T;
typedef unsigned long long uint64_T;
typedef float real32_T;
typedef double real64_T;

/*===========================================================================*
 * Generic type definitions: boolean_T, char_T, byte_T, int_T, uint_T,       *
 *                           real_T, time_T, ulong_T, ulonglong_T.           *
 *===========================================================================*/
typedef double real_T;
typedef double time_T;
typedef unsigned int boolean_T;
typedef int int_T;
typedef unsigned int uint_T;
typedef unsigned long ulong_T;
typedef unsigned long long ulonglong_T;
typedef char char_T;
typedef unsigned char uchar_T;
typedef char_T byte_T;

/*===========================================================================*
 * Complex number type definitions                                           *
 *===========================================================================*/
#define CREAL_T

typedef struct {
  real32_T re;
  real32_T im;
} creal32_T;

typedef struct {
  real64_T re;
  real64_T im;
} creal64_T;

typedef struct {
  real_T re;
  real_T im;
} creal_T;

#define CINT8_T

typedef struct {
  int8_T re;
  int8_T im;
} cint8_T;

#define CUINT8_T

typedef struct {
  uint8_T re;
  uint8_T im;
} cuint8_T;

#define CINT16_T

typedef struct {
  int16_T re;
  int16_T im;
} cint16_T;

#define CUINT16_T

typedef struct {
  uint16_T re;
  uint16_T im;
} cuint16_T;

#define CINT32_T

typedef struct {
  int32_T re;
  int32_T im;
} cint32_T;

#define CUINT32_T

typedef struct {
  uint32_T re;
  uint32_T im;
} cuint32_T;

#define CINT64_T

typedef struct {
  int64_T re;
  int64_T im;
} cint64_T;

#define CUINT64_T

typedef struct {
  uint64_T re;
  uint64_T im;
} cuint64_T;

/*=======================================================================*
 * Min and Max:                                                          *
 *   int8_T, int16_T, int32_T     - signed 8, 16, or 32 bit integers     *
 *   uint8_T, uint16_T, uint32_T  - unsigned 8, 16, or 32 bit integers   *
 *=======================================================================*/
#define MAX_int8_T                     ((int8_T)(127))
#define MIN_int8_T                     ((int8_T)(-128))
#define MAX_uint8_T                    ((uint8_T)(255U))
#define MAX_int16_T                    ((int16_T)(32767))
#define MIN_int16_T                    ((int16_T)(-32768))
#define MAX_uint16_T                   ((uint16_T)(65535U))
#define MAX_int32_T                    ((int32_T)(2147483647L))
#define MIN_int32_T                    ((int32_T)(-2147483647L-1L))
#define MAX_uint32_T                   ((uint32_T)(0xFFFFFFFFUL))
#define MAX_int64_T                    ((int64_T)(9223372036854775807LL))
#define MIN_int64_T                    ((int64_T)(-9223372036854775807LL-1LL))
#define MAX_uint64_T                   ((uint64_T)(0xFFFFFFFFFFFFFFFFULL))

/* Block D-Work pointer type */
typedef void * pointer_T;

#endif                                 /* RTWTYPES_H */

/*
 * File trailer for generated code.
 *
 * [EOF]
 */
