MUBARIS-KT/DC-DC_CONVERTER/pwm_ert_rtw/MW_c28xx_xbar.c

#include "c2000BoardSupport.h"
#include "MW_f2837xD_includes.h"
#include "rtwtypes.h"
#include "pwm.h"
#include "pwm_private.h"
#include "MW_c28xGPIO.h"

void configureIXbar(void)
{
  /*--- Configuring GPIO set in Input Xbar---*/
  EALLOW;
  InputXbarRegs.INPUT5SELECT = 0;
  EDIS;
}
