MUBARIS-KT/DC-DC_CONVERTER/PWM/pwm_ert_rtw/MW_c28xx_csl.c

#include "c2000BoardSupport.h"
#include "MW_f2837xD_includes.h"
#include "rtwtypes.h"
#include "pwm.h"
#include "pwm_private.h"

void enableExtInterrupt (void);
void configureGPIOExtInterrupt(void);

#include <stdint.h>

void disableWatchdog(void)
{
  int *WatchdogWDCR = (int *)(uintptr_t)0x7029;
  asm(" EALLOW ");
  *WatchdogWDCR = 0x0068;
  asm(" EDIS ");
}
